osamhack2020/APP_IoT_PowerManual_PowerManual/myapp/mdImg/벤치프레스 replace.png

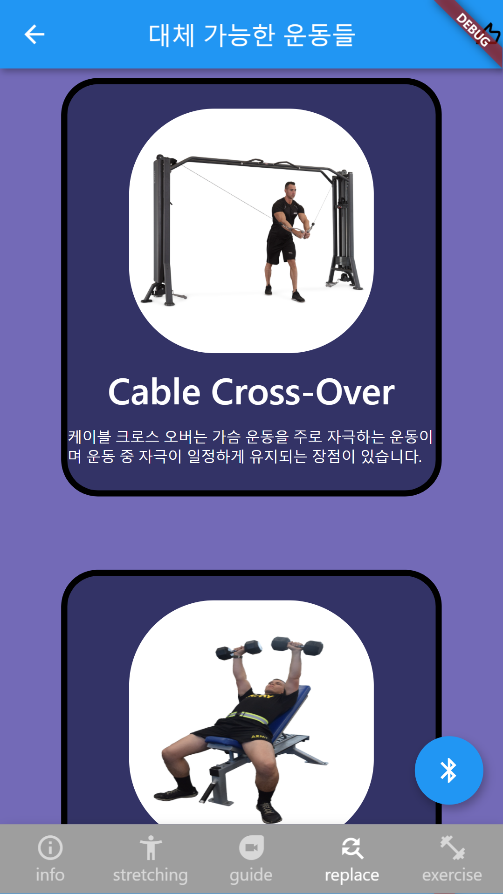
myapp/mdImg/벤치프레스 replace.png
