osamhack2020/APP_IoT_PowerManual_PowerManual/myapp/mdImg/벤치프레스 stretching.png

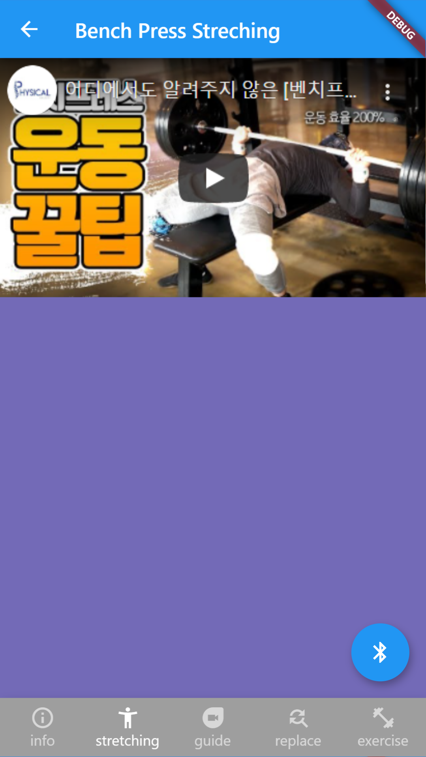
myapp/mdImg/벤치프레스 stretching.png
