osamhack2020/APP_IoT_PowerManual_PowerManual/myapp/mdImg/벤치프레스 guide.png

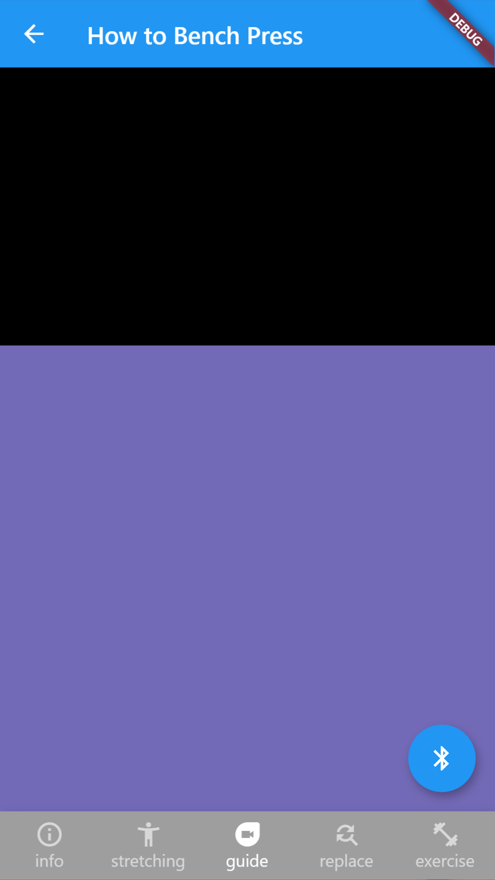
myapp/mdImg/벤치프레스 guide.png
