osamhack2020/APP_IoT_PowerManual_PowerManual/IoT(Arduino)/bluetooth/maintest.ino

//main
void setup() {
  setupmeasure();
  blue.begin(9600);
  MsTimer2::set(500,checking);//0.5초마다 명령이 들어왔는지,보낼것이 있는지 체크
  MsTimer2::start();
}

void loop() {
  if (flag){
    switch(exercise){
      case 1://squart 측정
        measureSquart();
      break;
//      case 2: //다른 운동일경우
//      measureSthelse();
//      break;
      default:
      blue.println('e');
  
  }
 }
 else{
  delay(500);
 }
}
